tonykoop/drone-flutes/inlay-patterns/Em/feature_constellation.dxf

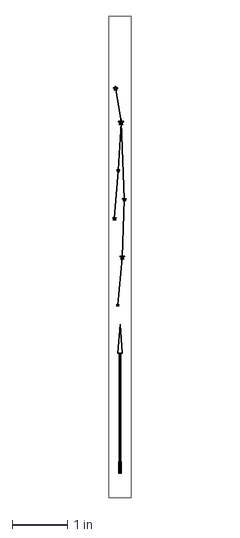
[picture p19: CAD file, 2026-05-05]
inlay-patterns/Em/feature_constellation.dxf
0.401 x 8.71 in
