tonykoop/drone-flutes/inlay-patterns/Fsharpm/band2_chevron.dxf

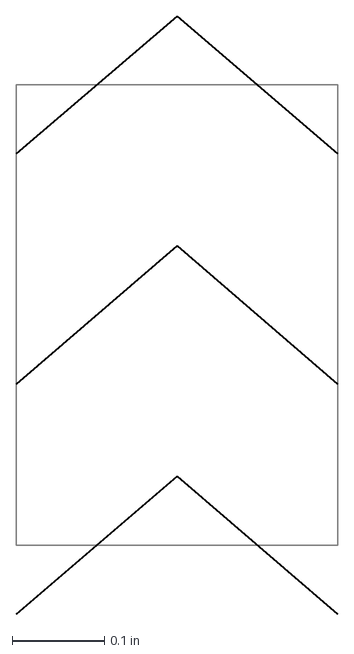
[picture p20: CAD file, 2026-05-05]
inlay-patterns/Fsharpm/band2_chevron.dxf
0.349 x 0.65 in
